luckyjkl/geiger-counter/software/HEADWARE/flash.h

#ifndef __FLASH_H
#define __FLASH_H			    
//#include "sys.h" 
#include "stm32f10x.h"
//////////////////////////////////////////////////////////////////////////////////	 
//本程序只供学习使用，未经作者许可，不得用于其它任何用途
//Mini STM32开发板
//W25X16 驱动函数	   
//正点原子@ALIENTEK
//技术论坛:www.openedv.com
//修改日期:2010/6/13 
//版本：V1.0
//版权所有，盗版必究。
//Copyright(C) 正点原子 2009-2019
//All rights reserved
////////////////////////////////////////////////////////////////////////////////// 	 
#define W25Q80 	0XEF13 	
#define W25Q16 	0XEF14
#define W25Q32 	0XEF15
#define W25Q64 	0XEF16
 

extern u16 SPI_FLASH_TYPE;		//定义我们使用的flash芯片型号

#define Flash_SPI_GPIO	GPIOB
#define Flash_GPIO_RCC	RCC_APB2Periph_GPIOB
#define Flash_SPI		SPI2
#define Flash_SPI_RCC	RCC_APB1Periph_SPI2
#define Flash_SPI_SCK	GPIO_Pin_13
#define Flash_SPI_MISO	GPIO_Pin_14
#define Flash_SPI_MOSI	GPIO_Pin_15

#define SPI_FLASH_CS_GPIO	GPIOB
#define SPI_FLASH_CS_RCC	RCC_APB2Periph_GPIOB
#define	SPI_FLASH_CS 		GPIO_Pin_12

#define SPI_FLASH_CS_HIGH	SPI_FLASH_CS_GPIO->BSRR = SPI_FLASH_CS
#define SPI_FLASH_CS_LOW	SPI_FLASH_CS_GPIO->BRR	= SPI_FLASH_CS
////////////////////////////////////////////////////////////////////////////

extern u8 SPI_FLASH_BUF[4096];
//W25X16读写
#define FLASH_ID 0XEF14
//指令表
#define W25X_WriteEnable		0x06 
#define W25X_WriteDisable		0x04 
#define W25X_ReadStatusReg		0x05 
#define W25X_WriteStatusReg		0x01 
#define W25X_ReadData			0x03 
#define W25X_FastReadData		0x0B 
#define W25X_FastReadDual		0x3B 
#define W25X_PageProgram		0x02 
#define W25X_BlockErase			0xD8 
#define W25X_SectorErase		0x20 
#define W25X_ChipErase			0xC7 
#define W25X_PowerDown			0xB9 
#define W25X_ReleasePowerDown	0xAB 
#define W25X_DeviceID			0xAB 
#define W25X_ManufactDeviceID	0x90 
#define W25X_JedecDeviceID		0x9F 

//void SPIx_SetSpeed(u8 SpeedSet);
u8 SPIx_ReadWriteByte(u8 TxData);

void SPI_Flash_Init(void);
u16  SPI_Flash_ReadID(void);  	    //读取FLASH ID
u8	 SPI_Flash_ReadSR(void);        //读取状态寄存器 
void SPI_FLASH_Write_SR(u8 sr);  	//写状态寄存器
void SPI_FLASH_Write_Enable(void);  //写使能 
void SPI_FLASH_Write_Disable(void);	//写保护
void SPI_Flash_Read(u8* pBuffer,u32 ReadAddr,u16 NumByteToRead);   //读取flash
void SPI_Flash_Write(u8* pBuffer,u32 WriteAddr,u16 NumByteToWrite);//写入flash
void SPI_Flash_Erase_Chip(void);    	  //整片擦除
void SPI_Flash_Erase_Sector(u32 Dst_Addr);//扇区擦除
void SPI_Flash_Wait_Busy(void);           //等待空闲
void SPI_Flash_PowerDown(void);           //进入掉电模式
void SPI_Flash_WAKEUP(void);			  //唤醒
#endif
